Han-ZenX/CLOCK/docs/hardware/high-end-frequency-counter-design.pdf

D E S I G N G U I D E · H I G H - E N D F R E Q U E N C Y C O U N T E R

# 高端频率计：功能定义、标准合规与研发全流程

本文给出一台高端台式频率计从指标定义到量产放行的完整路线：该具备哪些功能、关键指标怎么算、架构怎么分、要符合哪 些标准、怎么校准与验证。 公式与数值推算可以直接复用；标准编号与年份请以最新版本为准，标 推断 或 待确认 的内容需 要查原文核实。

对象 | 台式 / 机架式频率计
定位 | 计量级，可溯源
核心指标 | 单次分辨率、时基稳定度
日期 | 2026-09-16
用途 | 立项与方案设计

## 三个决定成败的判断

## 1 分辨率与时基，各管一段

短闸门由单次时间分辨率（TDC 插值）和触发噪声决定，长 闸门由时基稳定度决定，两者在某个闸门时间交叉。20 ps 分辨率配 1×10⁻¹² 的时基，交叉点约在 28 s。把钱花在交叉 点的另一侧没有意义。

## 2 能报阿伦方差才算高端

要输出可用于稳定度分析的数据，测量必须无死区、连续时 间戳，而且要清楚自己用的是哪种加权。Λ 型（加权平均） 计数器得到的数据不能直接当作阿伦方差报出，否则结论偏 乐观。

## 3 合规是设计输入，不是收尾

安全、EMC、计量型式批准的要求会反过来约束结构、接口 和电源设计。标准清单要在第 1 阶段就列出来（见第 8 页），临到试验才改设计代价最大。

## 本文导航

页 | 主题 | 你能从这一页得到什么
第 2 页 | 功能清单 | 基础测量、高级测量、分析与接口四类功能的完整列表，以及取舍建议
第 3 页 | 指标体系与误差预算 | 三项误差的计算公式、误差预算曲线、指标怎么定才自洽
第 4 页 | 系统架构 | 整机框图与各模块的设计要点
第 5 页 | 时间测量核心 | 倒数计数、插值与 TDC、连续时间戳、Π 与 Λ 加权的陷阱
第 6 页 | 输入前端与时基 | 前端电路设计要点、时基选型对照（OCXO / 铷钟 / GPSDO）
第 7 页 | 软件与接口 | 测量引擎、统计与稳定度分析、远程控制协议栈
第 8 页 | 国际标准 | 按用途分类的标准清单与合规路径
第 9 页 | 校准与验证 | 出厂校准、型式试验项目、不确定度评定方法
第 10 页 | 研发全流程 | 六个阶段、评审节点、并行工作与主要风险
高端频率计设计全流程 | 第 1 / 10 页

## 该具备哪些功能

按"没有就不算频率计""高端才有""决定能不能进实验室"三档划分。第三列给出取舍建议：功能越多，测量引擎和界面越复杂，不要一次全做。 一、基础测量（必备）

功能 | 说明 | 取舍
频率 / 周期 | 倒数计数，分辨率与闸门无关地 保持位数 | 核心
时间间隔 | 通道 1 起、通道 2 止，含通道间 时延校正 | 核心
脉宽 / 占空比 / 上升时间 | 同通道双沿或双电平触发 | 核心
频率比 | 两通道同时计数，不依赖时基精 度 | 低成本高价值
累计计数 | 门控或手动，用于事件计数 | 易实现
相位差 | 同频信号的相位，常用于比对 | 建议有
二、高端功能（区分档次）
功能 | 说明 | 取舍
连续时间戳输出 | 每个触发事件都带时标，无死区 | 高端核心
稳定度分析 | 阿伦方差及其改进型，趋势与直 方图 | 高端核心
调制域分析 | 频率随时间变化曲线，看跳频与 漂移 | 看目标市场
微波下变频 | 谐波混频或预分频，扩展到数十 GHz | 选件更合适
数学运算与限值判定 | 标度、偏差、上下限报警 | 软件实现

三、分析与数据（决定可用性）

功能 | 说明 | 取舍
统计 | 均值、标准差、最大最小、峰峰 值、样本数 | 必备
图形显示 | 趋势图、直方图、稳定度曲线 | 建议有
数据导出 | CSV 与二进制流，带时标与量纲 | 必备
不确定度提示 | 按当前设置给出本次测量的不确定 度估计 | 计量级建议有
自校准与自检 | 内部参考注入、TDC 线性度校正 | 必备

四、接口与系统集成

功能 | 说明 | 取舍
外部时基输入 / 输出 | 10 MHz 为主，兼容 5 MHz 更好 | 必备
远程控制 | LAN（LXI）、USBTMC、可选 GPIB | 必备
命令集 | SCPI，并提供 IVI 驱动 | 必备
外触发 / 门控 | 外部信号控制测量起止 | 建议有
1 PPS 输入 | 与 GPS 或主钟比对 | 计量场景必备
多机同步 | 共用时基与触发，做多通道扩展 | 看目标市场

建议的最小高端集：倒数计数 + 无死区连续时间戳 + 阿伦方差 + 外部时基 + SCPI/LXI + 自校准。其 余都可以作为选件或后续版本。

高端频率计设计全流程 | 第 2 / 10 页

## 指标体系与误差预算

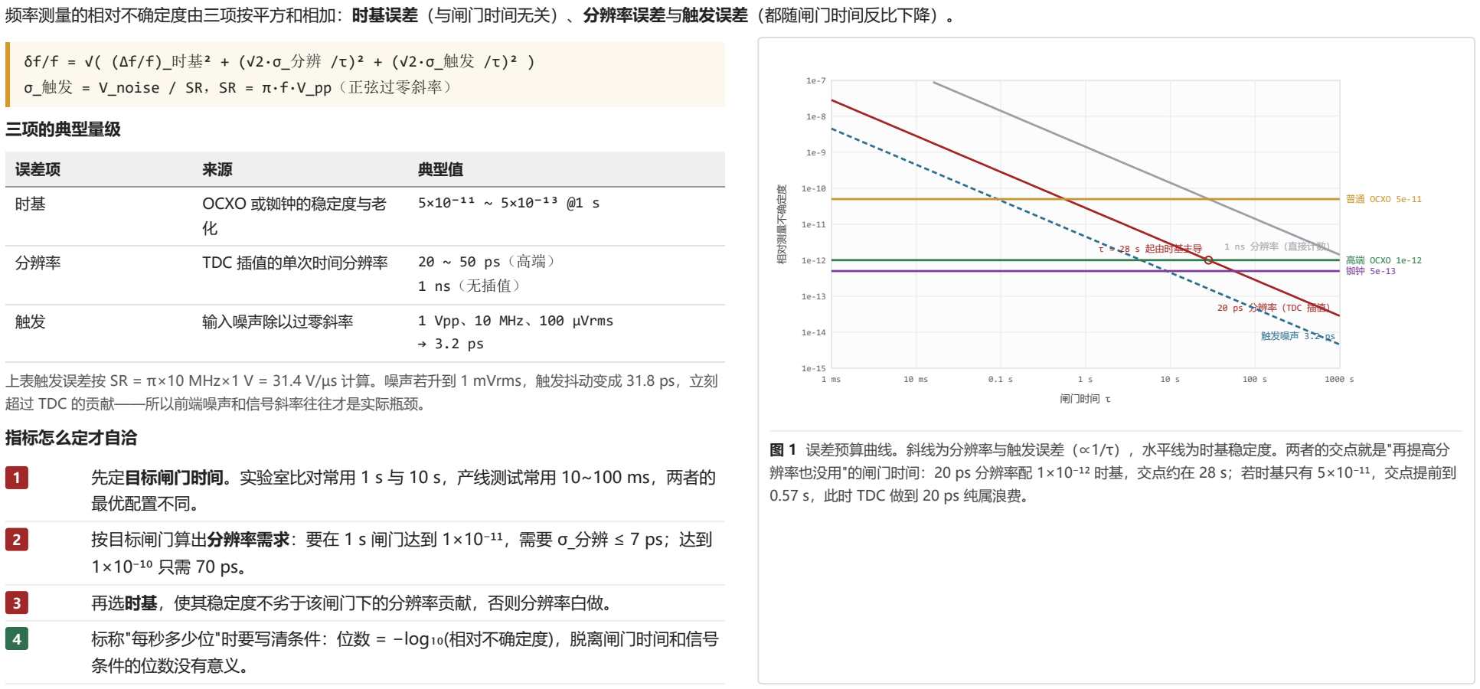
[picture p54: figure]
频率测量的相对不确定度由三项按平方和相加：时基误差（与闸门时间无关）、分辨率误差与触发误差（都随闸门时间反比下降）。; 三项的典型量级; 误差项; 典型值; OCXO 或铷钟的稳定度与老; 分辨率; TDC 插值的单次时间分辨率; 1 ns（无插值）; 输入噪声除以过零斜率; 1 Vpp、10 MHz、100 µVrms; 超过 TDC 的贡献——所以前端噪声和信号斜率往往才是实际瓶颈。 指标怎么定才自洽; 最优配置不同。; 3 再选时基，使其稳定度不劣于该闸门下的分辨率贡献，否则分辨率白做。; 4 标称"每秒多少位"时要写清条件：位数 = −log₁₀(相对不确定度)，脱离闸门时间和信号 条件的位数没有意义。; 1 ns 分辨率（直接计数）; 20 ps 分辨率（TDC 插值）; 触发噪声 3.2 ps; 普通 OCXO 5e-11; 高端 OCXO 1e-12 铷钟 5e-13; τ ≈ 28 s 起由时基主导; 闸门时间 τ; 0.57 s，此时 TDC 做到 20 ps 纯属浪费。

δf/f = √( (Δf/f)_时基² + (√2·σ_分辨 /τ)² + (√2·σ_触发 /τ)² ) σ_触发 = V_noise / SR，SR = π·f·V_pp（正弦过零斜率）

上表触发误差按 SR = π×10 MHz×1 V = 31.4 V/µs 计算。噪声若升到 1 mVrms，触发抖动变成 31.8 ps，立刻

### 1 先定目标闸门时间。实验室比对常用 1 s 与 10 s，产线测试常用 10~100 ms，两者的

### 2 按目标闸门算出分辨率需求：要在 1 s 闸门达到 1×10⁻¹¹，需要 σ_分辨 ≤ 7 ps；达到

图 1 误差预算曲线。斜线为分辨率与触发误差（∝1/τ），水平线为时基稳定度。两者的交点就是"再提高分 辨率也没用"的闸门时间：20 ps 分辨率配 1×10⁻¹² 时基，交点约在 28 s；若时基只有 5×10⁻¹¹，交点提前到

高端频率计设计全流程 | 第 3 / 10 页

## 系统架构

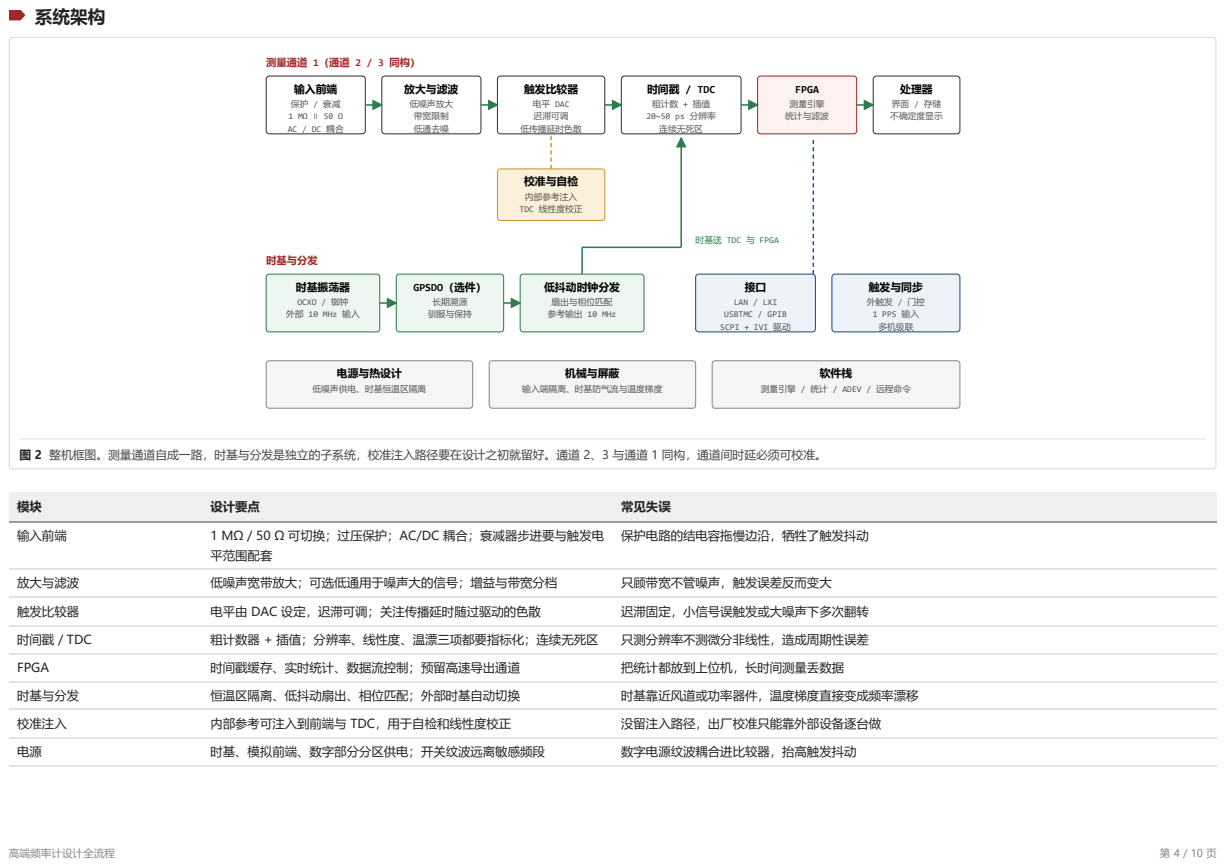
[picture p55: page 4]
放大与滤波; 低噪声放大 带宽限制 低通去噪; 触发比较器; 电平 DAC 迟滞可调 低传播延时色散; 时间戳 / TDC; 粗计数 + 插值 20~50 ps 分辨率 连续无死区; FPGA 测量引擎 统计与滤波; 处理器; 界面 / 存储 不确定度显示; 校准与自检; 内部参考注入 TDC 线性度校正; GPSDO（选件）; 长期溯源 驯服与保持; 低抖动时钟分发; 扇出与相位匹配 参考输出 10 MHz; 触发与同步; 外触发 / 门控 1 PPS 输入 多机级联; 电源与热设计; 低噪声供电、时基恒温区隔离; 机械与屏蔽; 输入端隔离、时基防气流与温度梯度; 软件栈; 设计要点; 常见失误; 输入前端; 1 MΩ / 50 Ω 可切换；过压保护；AC/DC 耦合；衰减器步进要与触发电; 平范围配套; 保护电路的结电容拖慢边沿，牺牲了触发抖动; 低噪声宽带放大；可选低通用于噪声大的信号；增益与带宽分档; 只顾带宽不管噪声，触发误差反而变大; 电平由 DAC 设定，迟滞可调；关注传播延时随过驱动的色散; 迟滞固定，小信号误触发或大噪声下多次翻转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

测量通道 1（通道 2 / 3 同构）
输入前端

时基送 TDC 与 FPGA

时基与分发
时基振荡器
OCXO / 铷钟
外部 10 MHz 输入

LAN / LXI
USBTMC / GPIB
SCPI + IVI 驱动

测量引擎 / 统计 / ADEV / 远程命令

图 2 整机框图。测量通道自成一路，时基与分发是独立的子系统，校准注入路径要在设计之初就留好。通道 2、3 与通道 1 同构，通道间时延必须可校准。

## 时间测量核心：从倒数计数到连续时间戳

### 1. 直接计数与倒数计数

直接计数在固定闸门内数被测信号的周期数，分辨率是 ±1 个周期，低频时位数很差（1 Hz 信号闸 门 1 s 只有 1 位）。倒数计数改为测量整数个周期所占的时间，分辨率与被测频率无关，是所有现 代频率计的基础。

### 2. 插值与 TDC

粗计数器的分辨率等于时基周期（100 MHz 时基即 10 ns）。要做到几十皮秒，必须对闸门首尾的 零头做插值。常见做法：

方法 | 典型分辨率 | 特点
模拟内插（时间拉伸） | 10 ~ 50 ps | 线性度好，速度慢，有死区
游标法 | 10 ~ 50 ps | 结构简单，转换时间长
延迟线 TDC（专用芯片） | 10 ~ 30 ps | 速度快，需温漂校正
FPGA 进位链 TDC | 20 ~ 50 ps | 成本低，微分非线性大，必须逐片校准

无论哪种，都要把分辨率、微分非线性、温度系数三项一起指标化。只标分辨率的 TDC 在长时间测量里会暴露周 期性误差。 推断

### 3. 死区时间

老式计数器在一次测量结束到下一次开始之间有死区，丢失的那段数据会让稳定度分析失真。高端 设计用连续时间戳：每个触发事件都打时标、连续送出，后续所有测量都由时标计算而来，天然无 死区。

最容易踩的坑：Π 型与 Λ 型加权
把闸门内的多个时间戳做最小二乘拟合或加权平均，可以把分辨率再提高一个量级，这类计数器称为 Λ 型（或 Ω 型）。但这种加权改变了测量的等效噪声带宽：用 Λ 型数据直接计算阿伦方差，结果会比真 实值乐观，对白频率噪声尤其明显。要报阿伦方差，必须用 Π 型（均匀权重）数据，或在软件里明确换 算并注明。这是高端频率计与稳定度分析仪的分界线之一。
推断，需按 IEEE 1139 与相关文献核实具体换算系数

### 4. 通道间时延与一致性

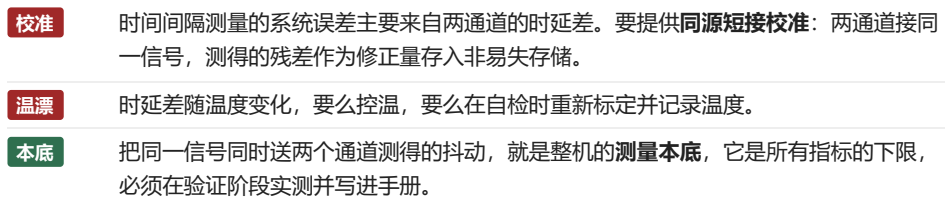
[picture p56: figure]
时间间隔测量的系统误差主要来自两通道的时延差。要提供同源短接校准：两通道接同; 一信号，测得的残差作为修正量存入非易失存储。; 时延差随温度变化，要么控温，要么在自检时重新标定并记录温度。; 把同一信号同时送两个通道测得的抖动，就是整机的测量本底，它是所有指标的下限，; 必须在验证阶段实测并写进手册。

### 5. 测量引擎的实现要点

环节 | 要点
时间戳缓存 | FPGA 内做环形缓冲，防止上位机卡顿导致丢点
数据率 | 高重复率信号下时间戳流量很大，需要抽取或硬件预处理
时标格式 | 足够位宽以避免长测量溢出，并带溢出标志
统计 | 均值、方差在 FPGA 内累加，避免传输全部原始数据
高端频率计设计全流程 | 第 5 / 10 页

## 输入前端与时基

输入前端设计要点

项目 | 设计取值 | 理由
输入阻抗 | 1 MΩ ∥ 低电容 与 50 Ω 可 切换 | 高阻接探头，50 Ω 接射频源并保证阻抗匹配
耦合方式 | AC / DC 可选 | AC 去除直流偏置，DC 用于慢信号与单次事件
衰减 | ×1 / ×10（或更多档） | 大信号不削顶，同时保住小信号的斜率
触发电平 | DAC 设定，覆盖全量程，分 辨率足够细 | 电平设在斜率最大处（正弦的过零点）可最小 化触发抖动
迟滞 | 可调，并提供自动设置 | 噪声大时防多次翻转，小信号时又不能太大
带宽限制 | 可选低通 | 被测信号带宽有限时，滤掉噪声直接降低触发 抖动
过压保护 | 钳位 + 限流，并给出最大输 入标称 | 50 Ω 档尤其脆弱，必须在规格书里写清功率上 限

前端的核心结论：触发抖动 = 输入噪声 ÷ 过零斜率。提高信号幅度、提高斜率、限制噪声带宽，三者 的收益都比换更贵的 TDC 直接。

时基选型对照

类型 | 1 s 稳定度 | 日老化 | 适用
普通 OCXO | 5×10⁻¹¹ 量级 | 1×10⁻⁹ 量级 | 入门机型
高端双烘箱 OCXO | 1×10⁻¹² 量级 | 1×10⁻¹⁰ 量级 | 主力配置
铷原子钟 | 5×10⁻¹³ 量级 | ≤1×10⁻¹¹ | 高端选件
外部时基输入 | 取决于外部源 | | 接实验室主钟或氢钟
GPSDO | 短期看被驯振荡器 | 长期趋近 UTC | 长期溯源

上表为典型量级， 推断 ，具体以所选型号手册为准。注意短期稳定度与长期溯源是两件事：GPSDO 解决长期， OCXO 或铷钟解决短期，高端机型常用 GPS 驯服高端 OCXO。
时基相关的设计细节
热 | OCXO 怕的是温度梯度和气流，不只是环境温度。要远离风道、电源和功率器件，必要
时加隔热罩。
电源 | 恒温槽加热电流是脉动的，供电路径与模拟前端分开，避免地回路耦合。
切换 | 外部时基接入要能自动检测、自动切换，并在界面明确指示当前时基来源与锁定状态。
老化 | 提供频率微调（DAC 或 DCO），配合校准周期修正老化；记录历史校准值可以预测下
次校准时间。
输出 提供 10 MHz 参考输出，方便与其它仪器共基准；输出与内部分发之间要隔离，防止外 部负载影响时基。
高端频率计设计全流程 | 第 6 / 10 页

## 软件、接口与远程控制

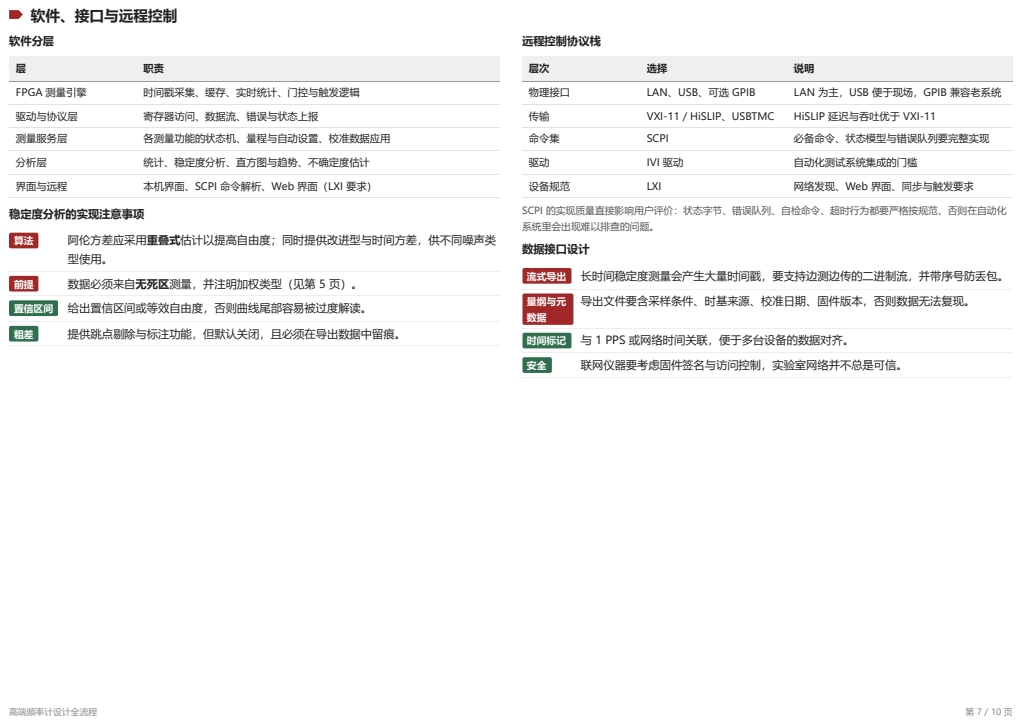
[picture p57: page 7]
软件分层; FPGA 测量引擎; 时间戳采集、缓存、实时统计、门控与触发逻辑; 驱动与协议层; 寄存器访问、数据流、错误与状态上报; 测量服务层; 各测量功能的状态机、量程与自动设置、校准数据应用; 分析层; 统计、稳定度分析、直方图与趋势、不确定度估计; 界面与远程; 本机界面、SCPI 命令解析、Web 界面（LXI 要求）; 稳定度分析的实现注意事项; 阿伦方差应采用重叠式估计以提高自由度；同时提供改进型与时间方差，供不同噪声类; 型使用。; 数据必须来自无死区测量，并注明加权类型（见第 5 页）。; 提供跳点剔除与标注功能，但默认关闭，且必须在导出数据中留痕。; 远程控制协议栈; 物理接口; LAN、USB、可选 GPIB; LAN 为主，USB 便于现场，GPIB 兼容老系统; VXI-11 / HiSLIP、USBTMC; HiSLIP 延迟与吞吐优于 VXI-11; 命令集; SCPI; 必备命令、状态模型与错误队列要完整实现; IVI 驱动; 自动化测试系统集成的门槛; 设备规范; LXI; 网络发现、Web 界面、同步与触发要求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

SCPI 的实现质量直接影响用户评价：状态字节、错误队列、自检命令、超时行为都要严格按规范，否则在自动化
系统里会出现难以排查的问题。
数据接口设计
流式导出 长时间稳定度测量会产生大量时间戳，要支持边测边传的二进制流，并带序号防丢包。

置信区间 给出置信区间或等效自由度，否则曲线尾部容易被过度解读。

量纲与元
时间标记 与 1 PPS 或网络时间关联，便于多台设备的数据对齐。

导出文件要含采样条件、时基来源、校准日期、固件版本，否则数据无法复现。

## 该符合哪些标准

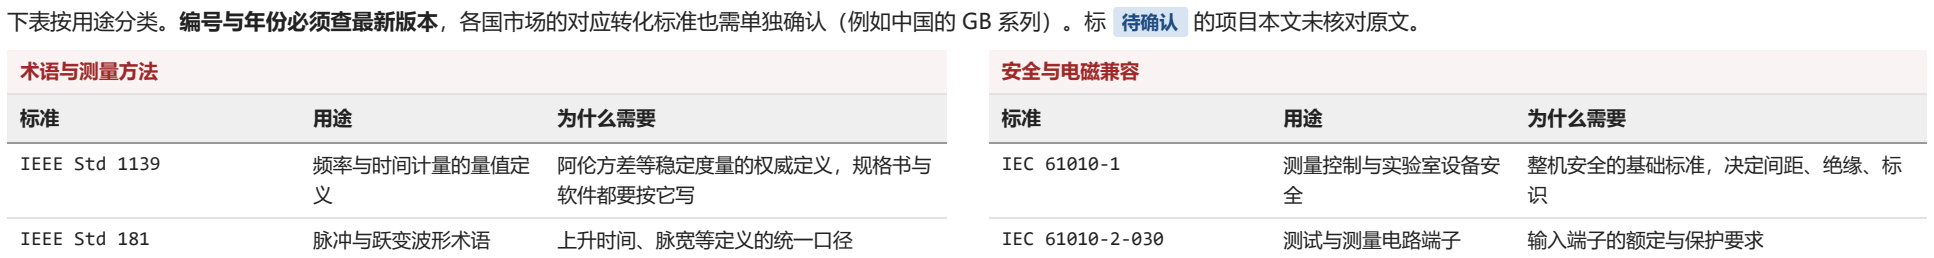
[picture p58: figure]
下表按用途分类。编号与年份必须查最新版本，各国市场的对应转化标准也需单独确认（例如中国的 GB 系列）。标 待确认 的项目本文未核对原文。; 术语与测量方法; 为什么需要; IEEE Std 1139; 频率与时间计量的量值定; 阿伦方差等稳定度量的权威定义，规格书与 软件都要按它写; IEEE Std 181; 脉冲与跃变波形术语; 上升时间、脉宽等定义的统一口径; 安全与电磁兼容; IEC 61010-1; 测量控制与实验室设备安; 整机安全的基础标准，决定间距、绝缘、标 识; IEC 61010-2-030; 测试与测量电路端子; 输入端子的额定与保护要求

ITU-T G.810 系列 | 同步网术语与漂移指标 | 若面向通信计量，MTIE / TDEV 的定义来 源

基准与溯源
ITU-T G.811 / G.8272 | 基准时钟等级 | 定义可作为溯源源的时钟性能
IEEE Std 1588 | 精密时间协议 | 网络化同步与时标关联
ISO/IEC 17025 | 校准实验室能力 | 出厂校准与售后校准体系的依据
ISO/IEC Guide 98-3（GUM） | 不确定度评定 | 规格书里的不确定度必须按它评定
JJF / JJG 相关规程 | 国内计量检定与校准 | 型式批准与周期检定依据 待确认具体编号
IEC 61326-1 | 测量设备 EMC 要求 | 抗扰度与发射的总要求，引用 CISPR 限值
CISPR 11 | 工科医设备骚扰限值 | 发射测试的具体限值与分类
IEC 61000-4 系列 | 抗扰度试验方法 | 静电、辐射、快速瞬变、浪涌等逐项试验
IEC 60068-2 系列 | 环境试验 | 温度、湿度、振动、冲击的试验方法
接口与系统集成
IEEE Std 488.1 / 488.2 | GPIB 与通用命令 | 命令语法、状态模型的基础
SCPI 规范 | 可编程仪器命令集 | 用户与自动化系统的通用语言
LXI 设备规范 | 以太网仪器 | 发现、Web 界面、触发与同步要求
IVI 规范 | 仪器驱动 | 进入自动化测试系统的门槛
USBTMC | USB 测试测量类 | USB 远程控制的标准实现

合规路径建议：第 1 阶段就确定目标市场，锁定安全与 EMC 的适用版本；第 3 阶段做设计自查（间 距、接地、屏蔽、端子标识）；第 4 阶段先做预测试，再进正式实验室，避免整改返工。计量型式批准 的周期往往最长，要最早启动。

高端频率计设计全流程 | 第 8 / 10 页

## 校准、验证与不确定度

验证项目清单

项目 | 方法 | 判据
测量本底 | 同一信号分路送两通道，或时基 自测 | 不劣于指标承诺的下限
单次分辨率 | 固定时间间隔重复测量，取标准 差 | 与 TDC 指标一致
TDC 线性度 | 扫描时间间隔，统计微分与积分 非线性 | 无周期性残差
触发抖动 | 改变输入幅度与斜率，测抖动随 斜率变化 | 符合 V_noise/SR 关系
时基稳定度 | 与更高等级基准比对，算阿伦方 差 | 达到时基手册指标
频率准确度 | 与铯钟或 GPS 驯服基准比对 | 在标称不确定度内
通道时延差 | 同源信号测时间间隔 | 残差可校准且稳定
温度特性 | 温箱内重复上述关键项 | 全温区满足指标
老化 | 长期连续记录时基频率 | 符合日老化与年老化承诺

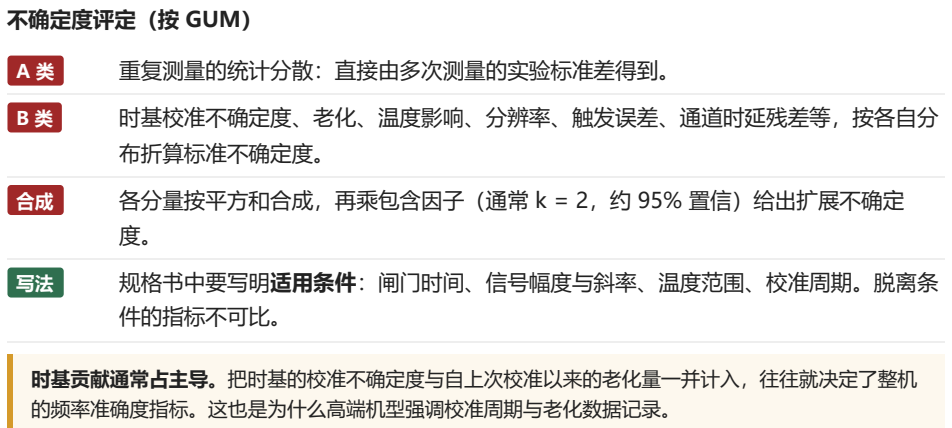
[picture p59: figure]
不确定度评定（按 GUM）; 重复测量的统计分散：直接由多次测量的实验标准差得到。; 时基校准不确定度、老化、温度影响、分辨率、触发误差、通道时延残差等，按各自分; 布折算标准不确定度。; 规格书中要写明适用条件：闸门时间、信号幅度与斜率、温度范围、校准周期。脱离条; 件的指标不可比。; 时基贡献通常占主导。把时基的校准不确定度与自上次校准以来的老化量一并计入，往往就决定了整机 的频率准确度指标。这也是为什么高端机型强调校准周期与老化数据记录。

合成 | 各分量按平方和合成，再乘包含因子（通常 k = 2，约 95% 置信）给出扩展不确定

出厂与售后

环节 | 内容
产线校准 | 时基频率调准、通道时延标定、TDC 线性度校正，结果写入非易失存储
校准证书 | 给出校准时的频率偏差与不确定度、溯源链、校准日期
周期检定 | 按计量规程规定周期（常见 12 个月）复校，并更新老化预测
自检 | 开机与按需自检：时基锁定、内部参考、TDC 自校、通道一致性
高端频率计设计全流程 | 第 9 / 10 页

## 研发全流程

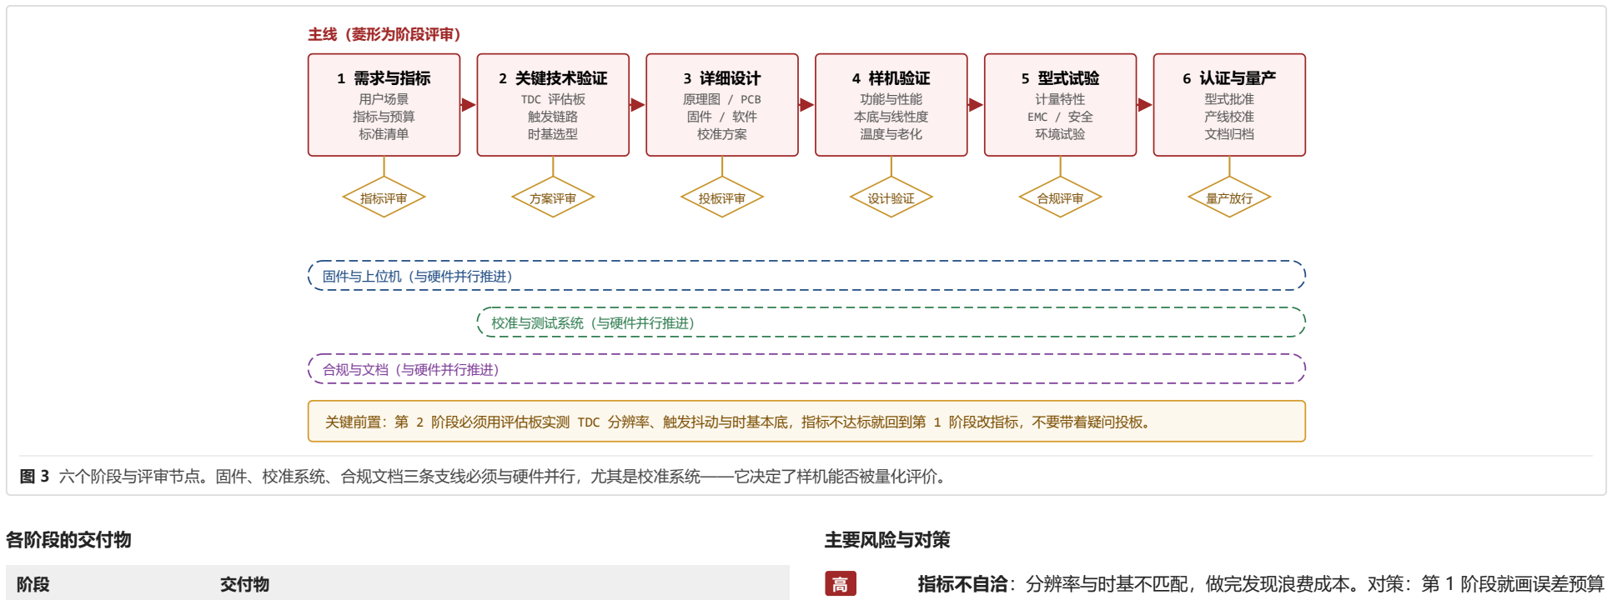
[picture p60: figure]
1 需求与指标; 用户场景 指标与预算 标准清单; 2 关键技术验证; TDC 评估板 触发链路 时基选型; 3 详细设计; 原理图 / PCB 固件 / 软件 校准方案; 4 样机验证; 功能与性能 本底与线性度 温度与老化; 5 型式试验; 计量特性 EMC / 安全 环境试验; 6 认证与量产; 型式批准 产线校准 文档归档; 指标评审; 方案评审; 投板评审; 设计验证; 合规评审; 量产放行; 固件与上位机（与硬件并行推进）; 校准与测试系统（与硬件并行推进）; 合规与文档（与硬件并行推进）; 主线（菱形为阶段评审）; 各阶段的交付物; 交付物; 主要风险与对策; 指标不自洽：分辨率与时基不匹配，做完发现浪费成本。对策：第 1 阶段就画误差预算

关键前置：第 2 阶段必须用评估板实测 TDC 分辨率、触发抖动与时基本底，指标不达标就回到第 1 阶段改指标，不要带着疑问投板。

图 3 六个阶段与评审节点。固件、校准系统、合规文档三条支线必须与硬件并行，尤其是校准系统——它决定了样机能否被量化评价。

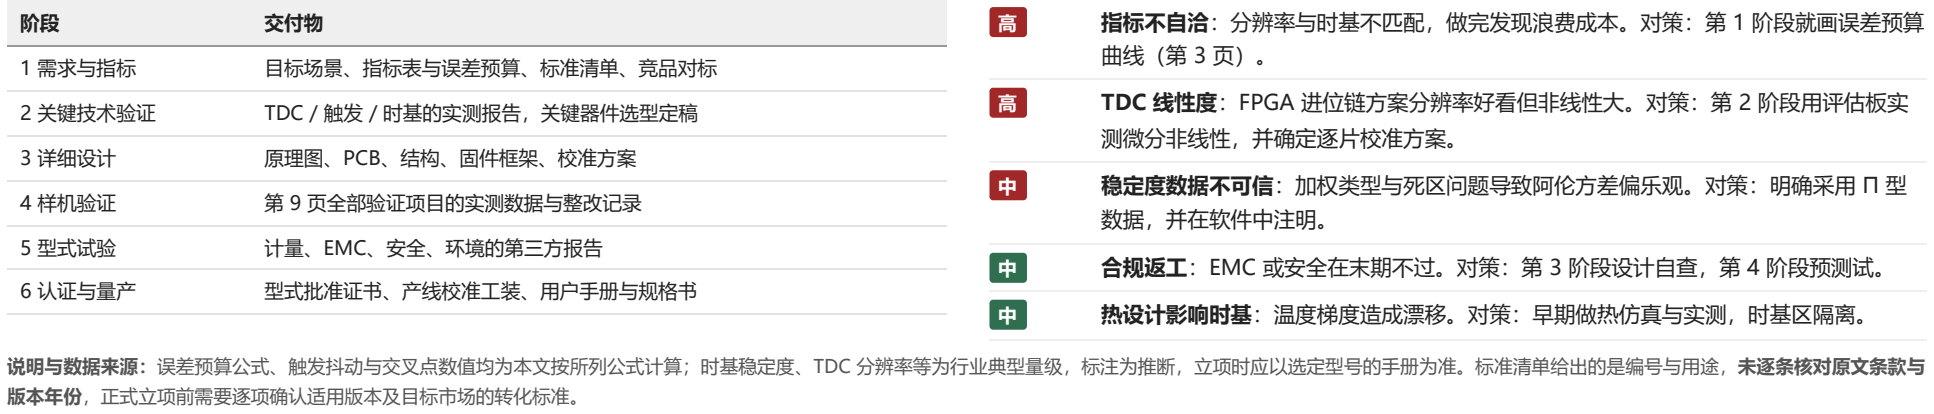
[picture p61: figure]
1 需求与指标; 目标场景、指标表与误差预算、标准清单、竞品对标; 2 关键技术验证; TDC / 触发 / 时基的实测报告，关键器件选型定稿; 3 详细设计; 原理图、PCB、结构、固件框架、校准方案; 4 样机验证; 第 9 页全部验证项目的实测数据与整改记录; 5 型式试验; 计量、EMC、安全、环境的第三方报告; 6 认证与量产; 型式批准证书、产线校准工装、用户手册与规格书; TDC 线性度：FPGA 进位链方案分辨率好看但非线性大。对策：第 2 阶段用评估板实; 测微分非线性，并确定逐片校准方案。; 稳定度数据不可信：加权类型与死区问题导致阿伦方差偏乐观。对策：明确采用 Π 型; 数据，并在软件中注明。; 热设计影响时基：温度梯度造成漂移。对策：早期做热仿真与实测，时基区隔离。; 说明与数据来源：误差预算公式、触发抖动与交叉点数值均为本文按所列公式计算；时基稳定度、TDC 分辨率等为行业典型量级，标注为推断，立项时应以选定型号的手册为准。标准清单给出的是编号与用途，未逐条核对原文条款与 版本年份，正式立项前需要逐项确认适用版本及目标市场的转化标准。

中 | 合规返工：EMC 或安全在末期不过。对策：第 3 阶段设计自查，第 4 阶段预测试。
高端频率计设计全流程 | 第 10 / 10 页
