Han-ZenX/CLOCK/docs/hardware/ocxo-vctrl-trimpot-fig.pdf

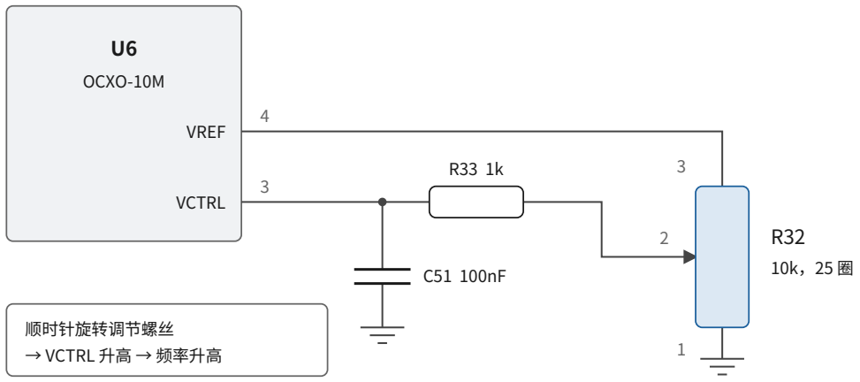
[picture p70: figure]
OCXO-10M; VREF; VCTRL; 顺时针旋转调节螺丝; → VCTRL 升高 → 频率升高
