Han-ZenX/CLOCK/docs/references/LDO/TPS7A52电源PCB布局.png

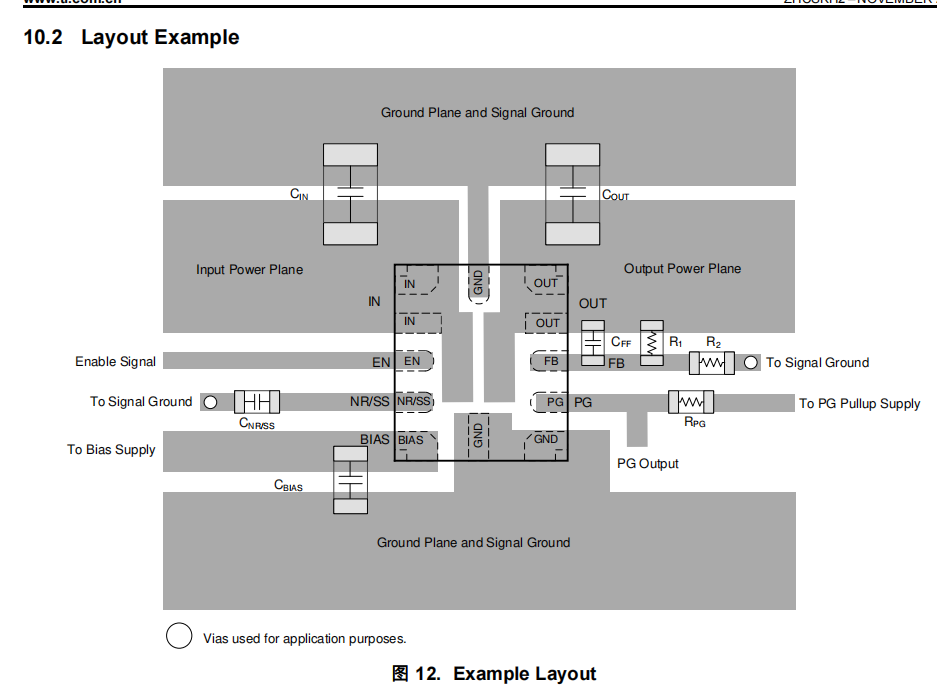
docs/references/LDO/TPS7A52电源PCB布局.png
