Han-ZenX/CLOCK/docs/references/SI5381A验证板.jpg

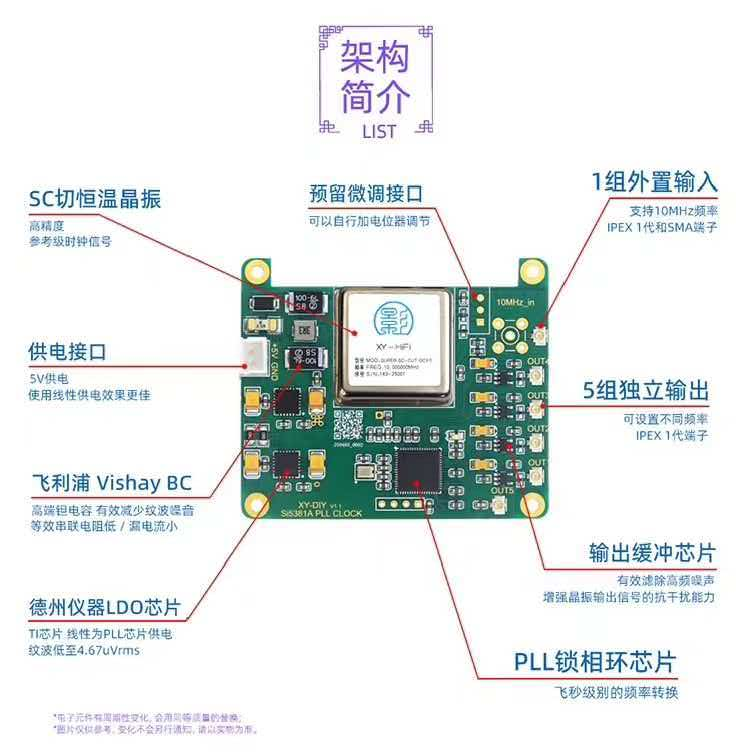
docs/references/SI5381A验证板.jpg
